Scottapotamas/HouseHound/WaterMonitor/src/WaterMonitor.ino

#include "Adafruit_ADS1X15.h"
#include "MQTT.h"
#include "RunningMedian.h"

#define LONG_TERM_AVERAGE_M 2
#define LONG_TERM_BUFFER_SIZE ((LONG_TERM_AVERAGE_M*60)*SENSOR_SAMPLE_PER_SECOND)

#define SENSOR_SAMPLE_PER_SECOND 2
#define SENSOR_SAMPLE_TIME_MS (1000/SENSOR_SAMPLE_PER_SECOND)

#define PUBLISH_RATE_S 10
#define PUBLISH_RATE_MS (PUBLISH_RATE_S*1000) //seconds into msec

// Timers to maintain sampling and publish throttles
unsigned int timeNextSensorReading;
unsigned int timeNextPublish;

Adafruit_ADS1115 ads;  /* Use this for the 16-bit version */

RunningMedian HeightBuffer = RunningMedian(LONG_TERM_BUFFER_SIZE);

void callback(char* topic, byte* payload, unsigned int length);

byte server[] = { 192,168,1,100 };
MQTT client(server, 1883, callback);

// recieve message
void callback(char* topic, byte* payload, unsigned int length)
{
  char p[length + 1];
  memcpy(p, payload, length);
  p[length] = NULL;
  delay(1000);
}

void setup(void)
{
  client.connect("watermonitor");

// publish/subscribe
  if (client.isConnected())
  {
    client.publish("debug/watermonitor","Starting Up");
  }

// The ADC input range (or gain) can be changed via the following
// functions, but be careful NEVER TO EXCEED +0.3V OVER VDD ON GAINED INPUTS,
// or exceed the upper and lower limits if you adjust the input range!
// Setting these values incorrectly may DESTROY your ADC!
//
//  *** TAKE CARE WHEN SETTING GAIN TO NOT EXCEED ABOVE LIMITS ON INPUT!!
//                                                                    ADS1015   ADS1115
//                                                                    -------   -------
ads.setGain(GAIN_TWOTHIRDS);  // 2/3x gain +/- 6.144V  1 bit =       3mV       0.1875mV (DEFAULT)
// ads.setGain(GAIN_ONE);        // 1x gain   +/- 4.096V  1 bit =     2mV       0.125mV
// ads.setGain(GAIN_TWO);        // 2x gain   +/- 2.048V  1 bit =     1mV       0.0625mV
// ads.setGain(GAIN_FOUR);       // 4x gain   +/- 1.024V  1 bit =     0.5mV     0.03125mV
// ads.setGain(GAIN_EIGHT);      // 8x gain   +/- 0.512V  1 bit =     0.25mV    0.015625mV
// ads.setGain(GAIN_SIXTEEN);    // 16x gain  +/- 0.256V  1 bit =     0.125mV   0.0078125mV
ads.begin();

timeNextSensorReading  = millis() + SENSOR_SAMPLE_TIME_MS;
timeNextPublish        = millis() + PUBLISH_RATE_MS;
}

void loop(void)
{
  if( timeNextSensorReading <= millis() )
  {
    sampleLevel();
    timeNextSensorReading = millis() + SENSOR_SAMPLE_TIME_MS; // Schedule the next sensor reading
  }

  // Publish the data collected to MQTT
  if( timeNextPublish <= millis() )
  {
    // Get the data to be published
    float tankHeight = getHeight();
    client.publish("enviro/tankDepthMM", String(tankHeight) );

    timeNextPublish = millis() + PUBLISH_RATE_MS;  // Schedule the next publish event
  }

  //connect to network
  if( client.isConnected() )
  {
    client.loop();
  }
  else
  {
    client.connect("weatherstation");
  }
}

void sampleLevel()
{
  double multiplier = 0.1875F; //milli Volts per bit for ADS1115

  short adc0_1 = ads.readADC_Differential_0_1();
  double av0_1 = adc0_1 * multiplier;

  HeightBuffer.add( convert_voltage_to_depth( av0_1 ) ); //add the latest value to the buffer
}

float getHeight()
{
  float result = HeightBuffer.getAverage();  //get the long term average

  return result;
}

float convert_voltage_to_depth(float milliVolts)
{
  float depth_in_mm = 0;

  //Curve from measured voltage vs depth information is
  // y = 1.6976x - 1465.5 where x is in mV
  depth_in_mm = (1.6976 * milliVolts) - 1465.5;

  if (depth_in_mm < 0)
  {
    depth_in_mm = 0;
  }

  return depth_in_mm;
}
